yagennankoz/PicoCMT/include/cmt_ui_input.h

#pragma once

void handle_file_browser_input();
void handle_wifi_menu_input();
void handle_rec_menu_input();
void handle_ui_buttons_in_standby();
void handle_wifi_config_input();
void handle_wifi_pin_connect_input();
void handle_wifi_connect_error_input();
void handle_playback_active_inputs(); 
